lwylonis/Autotune--EENG-348-Final-Design-Project/Amplifier PCB.kicad_sch

## KiCad design Amplifier PCB.kicad_sch (2025-06-22)

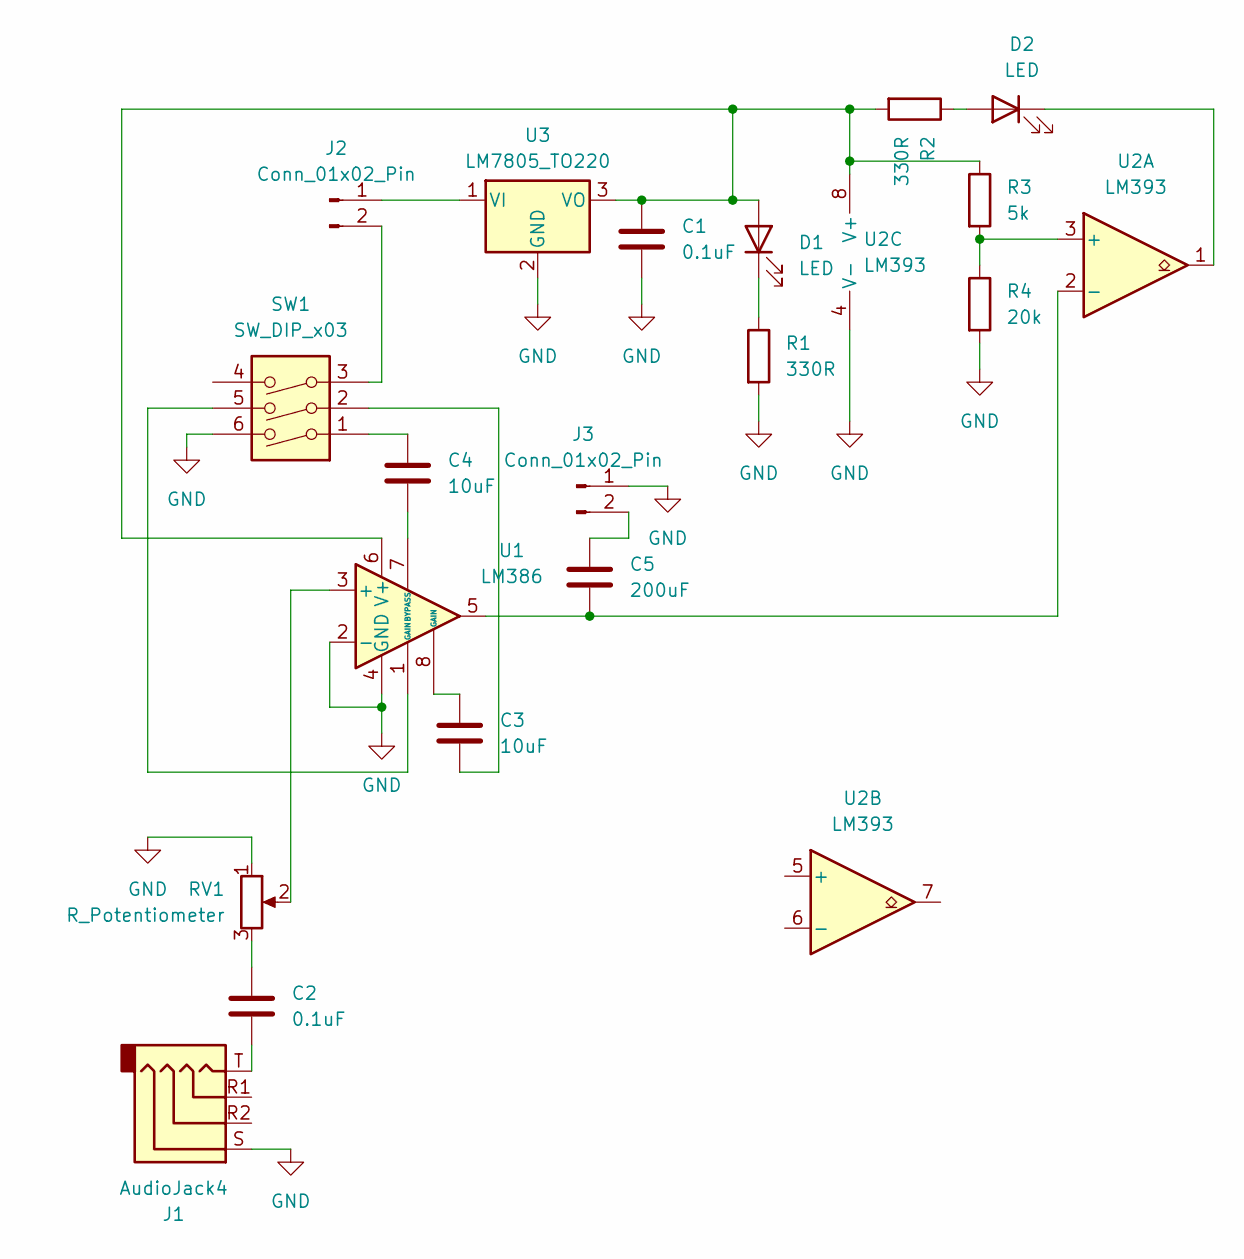
[picture p4: schematic Amplifier PCB.kicad_sch]

Parts:
C1, C2: 0.1uF; C_Disc_D5.0mm_W2.5mm_P5.00mm
C3, C4: 10uF; C_Radial_D5.0mm_H11.0mm_P2.00mm
C5: 200uF; C_Radial_D10.0mm_H12.5mm_P5.00mm
D1, D2: LED; LED_D5.0mm
J1: AudioJack4; Jack_3.5mm_CUI_SJ1-3523N_Horizontal
J2, J3: Conn_01x02_Pin; Samtec_HPM-02-01-x-S_Straight_1x02_Pitch5.08mm
R1, R2: 330R; R_Axial_DIN0207_L6.3mm_D2.5mm_P7.62mm_Horizontal
R3: 5k; R_Axial_DIN0207_L6.3mm_D2.5mm_P7.62mm_Horizontal
R4: 20k; R_Axial_DIN0207_L6.3mm_D2.5mm_P7.62mm_Horizontal
RV1: R_Potentiometer; Potentiometer_Bourns_PTV09A-1_Single_Vertical
SW1: SW_DIP_x03; SW_DIP_SPSTx03_Slide_6.7x9.18mm_W8.61mm_P2.54mm_LowProfile
U1: LM386; DIP-8_W7.62mm_Socket
U2: LM393; SOIC-8-1EP_3.9x4.9mm_P1.27mm_EP2.29x3mm
U3: LM7805_TO220; TO-220-3_Vertical

Connections:
GND: C1.2, J1.S, J3.1, R1.2, R4.2, RV1.1, SW1.6, U1.2 (-), U1.4 (GND), U2.4 (V-), U3.2 (GND)
unnamed: C1.1, D1.2 (A), R2.2, R3.1, U1.6 (V+), U2.8 (V+), U3.3 (VO)
unnamed: C2.1, RV1.3
unnamed: C2.2, J1.T
unnamed: C3.1, U1.8 (GAIN)
unnamed: C3.2, SW1.2
unnamed: C4.1, SW1.1
unnamed: C4.2, U1.7 (BYPASS)
unnamed: C5.1, J3.2
unnamed: C5.2, U1.5, U2.2 (-)
unnamed: D1.1 (K), R1.1
unnamed: D2.1 (K), U2.1
unnamed: D2.2 (A), R2.1
unnamed: J2.1, U3.1 (VI)
unnamed: J2.2, SW1.3
unnamed: R3.2, R4.1, U2.3 (+)
unnamed: RV1.2, U1.3 (+)
unnamed: SW1.5, U1.1 (GAIN)
